SHIMA-R7/SHVC-SOUND-Player/SHVC-SOUND_python/spc_play.py

#!/usr/bin/env python3
"""
spc_play.py - .spcファイルをSHVC-SOUND(実チップ)で再生する

Arduino側は spc_uploader.ino (シリアルコマンド版) を書き込んでおくこと。

使い方:
    pip install pyserial
    python spc_play.py COM3 song.spc      (Windows)
    python spc_play.py /dev/ttyACM0 song.spc  (Linux)

.spcファイル形式(オフセットは既知の標準フォーマット):
    0x00-0x20 : ヘッダ("SNES-SPC700 Sound File Data v0.30" 等)
    0x25-0x26 : PC (リトルエンディアン)
    0x27      : A
    0x28      : X
    0x29      : Y
    0x2A      : PSW
    0x2B      : SP
    0x100-0x100FF : ARAM 64KB ダンプ
    0x10100-0x1017F : DSPレジスタ 128バイト
"""

import sys
import time
import serial

CMD_RESET = 0x01
CMD_SETADDR = 0x02
CMD_SENDBYTES = 0x03
CMD_READPORT = 0x04
CMD_SETVOLUME = 0x05
CMD_WRITEPORT = 0x0B

# 曲開始前の待ち合わせ(build_final_stub の port_handshake 参照)
STUB_MARK_STARTED = 0x99
STUB_MARK_WAITING = 0x98

ACK_RESET = 0x01
ACK_SETADDR = 0x02
ACK_CHUNK = 0x10
ACK_SENDBYTES = 0x03


class TransferCancelled(Exception):
    """転送がユーザー操作で中断されたことを示す。"""


def _decode_tag(raw: bytes) -> str:
    """ID666タグの文字列フィールドをデコードする。NUL以降は切り捨てる。"""
    raw = raw.split(b"\x00", 1)[0]
    for enc in ("cp932", "utf-8", "latin-1"):
        try:
            return raw.decode(enc).strip()
        except UnicodeDecodeError:
            continue
    return ""


class SpcFile:
    def __init__(self, path):
        with open(path, "rb") as f:
            data = f.read()
        if len(data) < 0x10180:
            raise ValueError(".spcファイルとして小さすぎます(壊れているかも)")

        # --- ID666タグ(あれば) ---
        # 0x23 が 26(0x1A) ならタグあり、27(0x1B) ならタグなし。
        # ここではテキスト形式のオフセットで読む(最も一般的な形式)。
        self.tags = {}
        if data[0x23] == 0x1A:
            self.tags = {
                "title": _decode_tag(data[0x2E:0x4E]),
                "game": _decode_tag(data[0x4E:0x6E]),
                "dumper": _decode_tag(data[0x6E:0x7E]),
                "comment": _decode_tag(data[0x7E:0x9E]),
                "date": _decode_tag(data[0x9E:0xA9]),
                "seconds": _decode_tag(data[0xA9:0xAC]),
                "artist": _decode_tag(data[0xB1:0xD1]),
            }

        self.pc = data[0x25] | (data[0x26] << 8)
        self.a = data[0x27]
        self.x = data[0x28]
        self.y = data[0x29]
        self.psw = data[0x2A]
        self.sp = data[0x2B]

        self.ram = data[0x100:0x100 + 0x10000]           # 64KB
        self.dsp = data[0x10100:0x10100 + 0x80]           # 128バイト


class SpcController:
    def __init__(self, port, baud=500000, log=None, progress=None):
        """
        log      : log(msg:str) 進行状況の文字列を受け取るコールバック
        progress : progress(done:int, total:int) 転送済み/全体バイト数
        いずれも省略時は標準出力へprint / 何もしない。
        """
        self.log = log if log is not None else print
        self.on_progress = progress if progress is not None else (lambda d, t: None)
        # 全体進捗の集計用。play()が転送開始前にtotal_bytesを設定する。
        self.total_bytes = 0
        self.done_bytes = 0

        self.ser = serial.Serial(port, baud, timeout=10)
        time.sleep(2)  # Arduinoのリセット待ち(DTRでリセットがかかる環境向け)
        self.ser.reset_input_buffer()

    def close(self):
        try:
            self.ser.close()
        except Exception:
            pass

    def _read_ack(self, expected):
        b = self.ser.read(1)
        if len(b) != 1 or b[0] != expected:
            raise RuntimeError(f"想定外の応答: {b!r} (期待値 0x{expected:02X})")

    def reset(self):
        self.log("SPC700をリセットしてready待ち...")
        self.ser.write(bytes([CMD_RESET]))
        self._read_ack(ACK_RESET)
        self.log("SPC700 ready.")

    def set_address(self, addr, continue_transfer):
        self.ser.write(bytes([CMD_SETADDR, addr & 0xFF, (addr >> 8) & 0xFF,
                               1 if continue_transfer else 0]))
        b = self.ser.read(1)
        if len(b) == 1 and b[0] == 0xEE:
            rest = self.ser.read(4)
            if len(rest) == 4 and rest[0] == 0xFF and rest[1] == 0xFF:
                raise RuntimeError(f"SETADDRがタイムアウト: addr=${addr:04X}")
            raise RuntimeError(f"SETADDR異常応答: {rest!r}")
        if len(b) != 1 or b[0] != ACK_SETADDR:
            raise RuntimeError(f"想定外の応答: {b!r} (期待値 0x{ACK_SETADDR:02X})")

    def send_bytes(self, data):
        length = len(data)
        self.ser.write(bytes([CMD_SENDBYTES, length & 0xFF, (length >> 8) & 0xFF]))

        diag = self.ser.read(3)
        if len(diag) != 3 or diag[0] != 0xAB:
            raise RuntimeError(f"len診断応答が異常: {diag!r} (送った長さ={length})")
        echoed_len = diag[1] | (diag[2] << 8)
        if echoed_len != length:
            raise RuntimeError(f"lenが化けた! 送った長さ={length}, Arduinoが受け取った長さ={echoed_len}")

        # Arduinoのシリアル受信バッファ(64バイト)を溢れさせないよう
        # PING_INTERVAL(Arduino側と一致させること)バイトずつ送って
        # 「まとめて1回だけ」確認応答を待つ。
        #
        # かつては1バイト送るごとに1往復のUSBシリアル通信が発生しており、
        # 実機計測で65216バイトの転送に約38秒かかっていた(バイト単位の
        # bit伝送時間ではなく、USB経由のシリアル往復レイテンシが支配的
        # だった)。往復回数を1/PING_INTERVALに減らすことで大幅に短縮する。
        PING_INTERVAL = 64
        pos = 0
        while pos < length:
            chunk_len = min(PING_INTERVAL, length - pos)
            self.ser.write(data[pos:pos + chunk_len])

            marker = self.ser.read(1)
            if len(marker) != 1:
                raise RuntimeError(f"応答なし(タイムアウト)。進捗={pos}/{length}")
            if marker[0] == 0xEE:
                rest = self.ser.read(4)
                idx = rest[0] | (rest[1] << 8)
                raise RuntimeError(
                    f"転送中にタイムアウト: バイト位置 {idx}/{length} で停止。"
                    f"送信した値=0x{rest[2]:02X}, 期待した応答=0x{idx & 0xFF:02X}, "
                    f"実際に読めた値=0x{rest[3]:02X}"
                )
            if marker[0] != 0xCD:
                raise RuntimeError(f"想定外の応答バイト: 0x{marker[0]:02X} (進捗={pos}/{length})")

            pos += chunk_len
            total = self.total_bytes or length
            self.on_progress(self.done_bytes + pos, total)
            if pos % (PING_INTERVAL * 5) == 0 or pos == length:
                self.log(f"    進捗: {pos}/{length} バイト転送済み")

        final = self.ser.read(1)
        if len(final) != 1 or final[0] != ACK_SENDBYTES:
            raise RuntimeError(f"最終応答が想定外: {final!r}")

    def write_block(self, addr, data):
        self.set_address(addr, True)
        self.send_bytes(data)

    def jump_to(self, addr):
        self.set_address(addr, False)

    def write_port(self, port, val):
        self.ser.write(bytes([CMD_WRITEPORT, port & 0x03, val & 0xFF]))
        b = self.ser.read(1)
        if len(b) != 1 or b[0] != CMD_WRITEPORT:
            raise RuntimeError(f"write_port応答が異常: {b!r} (spc_realtime.inoが古い可能性)")

    def wait_port(self, port, values, timeout=2.0):
        """ポートの値が values のどれかになるまで待ち、その値を返す。"""
        deadline = time.time() + timeout
        while True:
            v = self.read_port(port)
            if v in values or time.time() > deadline:
                return v

    def read_port(self, port):
        self.ser.write(bytes([CMD_READPORT, port]))
        resp = self.ser.read(2)
        if len(resp) != 2 or resp[0] != 0x04:
            raise RuntimeError(f"read_port応答が異常: {resp!r}")
        return resp[1]

    def set_volume(self, duty):
        """
        TDA7053AのVC1/VC2へつながるPWM(Arduino D10)のデューティ比を設定する。
        duty は 0(無音側)〜255(最大音量側)。R5/R6/C5の分圧値が未校正の場合、
        実際に0.4V以下/1.4V以上になる値は現物合わせで探る必要がある
        (PROJECT_BRIEF.md 3.4節・5節参照)。
        """
        duty = max(0, min(255, int(duty)))
        self.ser.write(bytes([CMD_SETVOLUME, duty]))
        resp = self.ser.read(2)
        if len(resp) != 2 or resp[0] != CMD_SETVOLUME:
            raise RuntimeError(f"set_volume応答が異常: {resp!r}")
        return resp[1]


def boost_master_volume(dsp: bytes, factor: float) -> bytes:
    """
    マスター音量(MVOLL/MVOLR)と各ボイスのVOLL/VOLRをまとめて底上げした
    DSPレジスタ配列を返す(元は変更しない)。

    S-DSPの音量レジスタは符号付き8bit(-128〜127)。正の値が大きいほど
    音量が大きい(負値は位相反転付きの音量で、曲データで意図的に使われる
    ことがあるため符号は保持する)。単純に factor 倍して、
    signed 8bit の範囲(-128〜127)でクランプする。

    マスター音量(MVOLL/MVOLR)は多くの曲で既に127(最大)近くまで
    使われているため、そこだけ底上げしても頭打ちで変化が出にくい。
    実際に鳴っている音量を支配しているのは各ボイスのVOLL/VOLR($x0/$x1,
    x=0-7のボイス番号)なので、そちらも同じ倍率で底上げする。
    """
    out = bytearray(dsp)
    regs = [0x0C, 0x1C]                              # MVOLL, MVOLR
    regs += [v * 0x10 + off for v in range(8) for off in (0x00, 0x01)]  # 各ボイスVOLL/VOLR
    for reg in regs:
        raw = dsp[reg]
        signed = raw - 256 if raw >= 128 else raw
        boosted = round(signed * factor)
        boosted = max(-128, min(127, boosted))
        out[reg] = boosted & 0xFF
    return bytes(out)


def handshake_values(spc: SpcFile):
    """
    曲開始前の待ち合わせに使う (開始合図, 最終的な$F4の値) を返す。
    開始合図は、曲が期待する$F4の値と必ず異なるものを選ぶ。
    """
    final_f4 = spc.ram[0xF4]
    signal = 0x5A if final_f4 != 0x5A else 0xA5
    return signal, final_f4


def build_final_stub(spc: SpcFile, force_test_tone: bool = False, volume_factor: float = 1.0,
                     port_handshake: bool = False) -> bytes:
    """
    DSPレジスタ128個・コントロール/タイマー・CPUレジスタをすべて復元して
    実行を開始する、SPC700側で実際に動くコード。

    メモリマップドI/O($F2/$F3等)への直接アドレス指定書き込みは信頼できない
    ことが実機で確認できたため、SPC700自身に「mov $F2,#idx / mov $F3,#val」を
    実行させる。このコードは高位アドレス($FFC0直下)に置く。

    ※既知の制限: スタブは約800バイトあり、$FFC0直下ということは
      $FC9x-$FFBF付近を占める。この領域はメインRAM転送($0100-$FFBF)の
      範囲内なので、曲データを800バイト分上書きしてしまう。
      この領域をサンプルデータやエコーバッファに使っている曲では
      ノイズや音の破綻が出る。要対策(スタブのループ化+テーブル参照で
      小型化する / エコーバッファ領域に置く 等)。

    最後に $00/$01 の実データを書き戻し、SP/PSW/A/X/Y を復元して
    本来のPCへジャンプする(Wikibooks "Loading SPC700 programs" の手法)。

    force_test_tone=True の場合、曲データ復元の直後に強制的にノイズテスト用の
    レジスタ上書きを追加する(診断用: 経路自体が生きているか確認するため)。
    """
    stub = bytearray()

    dsp = spc.dsp if volume_factor == 1.0 else boost_master_volume(spc.dsp, volume_factor)

    # 診断: スタブが実際に実行開始されたか確認するためのマーカー。
    # 実行されれば$F4(host側から見てport0)に0x99が現れるはず。
    stub += bytes([0x8F, 0x99, 0xF4])  # mov $F4,#0x99

    # DSPレジスタ128個を復元する。順序が重要:
    #  1. FLG($6C)にまず $20 を書く。soft reset(bit7)とmute(bit6)を解除しつつ、
    #     エコー書き込みは禁止(bit5=1)のままにする。ここで曲の保存値をそのまま
    #     書いてしまうと、ESA($6D)/EDL($7D)を設定する前にDSPがエコーデータを
    #     ARAMへ書き始め、転送済みの曲データを破壊する(特にEDL=0のときは
    #     エコーバッファ先頭4バイトを延々と上書きし続ける)。
    #  2. FLG/KON以外の126個を復元(この中でESA/EDLが正しい値になる)。
    #  3. KON($4C)を書いてキーオン。
    #  4. 最後にFLG($6C)へ保存値を書き、必要ならエコーを有効化する。
    stub += bytes([0x8F, 0x6C, 0xF2])
    stub += bytes([0x8F, 0x20, 0xF3])

    order = [i for i in range(0x80) if i not in (0x6C, 0x4C)] + [0x4C]
    for i in order:
        stub += bytes([0x8F, i, 0xF2])
        stub += bytes([0x8F, dsp[i], 0xF3])

    stub += bytes([0x8F, 0x6C, 0xF2])
    stub += bytes([0x8F, dsp[0x6C], 0xF3])

    # コントロールレジスタ・タイマー分周値を復元
    stub += bytes([0x8F, spc.ram[0xF1], 0xF1])
    stub += bytes([0x8F, spc.ram[0xFA], 0xFA])
    stub += bytes([0x8F, spc.ram[0xFB], 0xFB])
    stub += bytes([0x8F, spc.ram[0xFC], 0xFC])

    if force_test_tone:
        # 診断用: 以前成功したノイズテストと同じ強制上書き
        test_pokes = [
            (0x6C, 0x0A),  # FLG: mute=0,reset=0, ノイズクロック=0x0A
            (0x0C, 0x60),  # MVOLL
            (0x1C, 0x60),  # MVOLR
            (0x3D, 0x01),  # NON: ボイス0でノイズ有効
            (0x00, 0x7F),  # ボイス0 VOLL
            (0x01, 0x7F),  # ボイス0 VOLR
            (0x05, 0x00),  # ボイス0 ADSR1無効(GAIN直接モード)
            (0x07, 0x7F),  # ボイス0 GAIN最大
            (0x4C, 0x01),  # KON: ボイス0キーオン
        ]
        for idx, val in test_pokes:
            stub += bytes([0x8F, idx, 0xF2])
            stub += bytes([0x8F, val, 0xF3])
        # テストモードでは本来のCPUレジスタ復元・ジャンプはせず自己ループで停止
        stub += bytes([0x2F, 0xFE])  # BRA自己ループ
        return bytes(stub)

    if port_handshake:
        # 曲のプログラムは$F4-$F7を「ゲーム本体からの指示」として読む。
        # ジャンプ直後のポートにはIPL転送で使ったジャンプ先アドレス等が残っていて、
        # それを指示と解釈して壊れる曲がある(SimCity等。毎回同じ壊れ方をする)。
        # そこで曲へ飛ぶ前にホストを待ち、SPCファイルに記録された入力値を
        # 置いてもらってから開始する。
        #   1. $F4 に開始合図が来るまで待つ(ホストはその前に$F5-$F7を書く)
        #   2. $F4へ0x98を出して「待機中」を知らせる
        #   3. $F4 が曲の期待値になるまで待つ
        signal, final_f4 = handshake_values(spc)
        stub += bytes([0x78, signal, 0xF4, 0xD0, 0xFB])            # cmp $F4,#signal / bne 自分
        stub += bytes([0x8F, STUB_MARK_WAITING, 0xF4])             # mov $F4,#$98
        stub += bytes([0x78, final_f4, 0xF4, 0xD0, 0xFB])          # cmp $F4,#final / bne 自分

    # CPUレジスタ復元+ジャンプ
    # $00/$01 はメインRAM転送であえてスキップしている
    # (IPL ROMが転送中にこの2バイトを内部の転送先ポインタとして使うため)ので、
    # ここで実データを明示的に書き戻す。
    stub += bytes([0x8F, spc.ram[0x00], 0x00])   # mov $00,#byte0
    stub += bytes([0x8F, spc.ram[0x01], 0x01])   # mov $01,#byte1
    stub += bytes([0xCD, spc.sp])        # mov x,#sp
    stub += bytes([0xBD])                # mov sp,x
    stub += bytes([0xCD, spc.psw])       # mov x,#psw
    stub += bytes([0x4D])                # push x
    stub += bytes([0xE8, spc.a])         # mov a,#a
    stub += bytes([0xCD, spc.x])         # mov x,#x
    stub += bytes([0x8D, spc.y])         # mov y,#y
    stub += bytes([0x8E])                # pop psw
    stub += bytes([0x5F, spc.pc & 0xFF, (spc.pc >> 8) & 0xFF])  # jmp !abs pc

    return bytes(stub)


def play(port, spc_path, force_test_tone=False, skip_bulk=False, low_addr=False, only_stub=False,
         volume_factor=1.0, amp_volume=None, log=None, progress=None, cancelled=None):
    """
    log       : log(msg:str)                 進行状況の文字列
    progress  : progress(done:int, total:int) 転送済み/全体バイト数
    cancelled : cancelled() -> bool           Trueを返すと転送を中断する
    """
    log = log if log is not None else print
    spc = SpcFile(spc_path)
    ctl = SpcController(port, log=log, progress=progress)

    def check_cancel():
        if cancelled is not None and cancelled():
            raise TransferCancelled()

    try:
        ctl.reset()
        check_cancel()

        # 復元スタブを先に作っておく(全体バイト数を進捗表示に使うため)
        handshake = not force_test_tone
        stub = build_final_stub(spc, force_test_tone=force_test_tone,
                                volume_factor=volume_factor, port_handshake=handshake)

        head = spc.ram[0x0002:0x00F0]
        bulk = b"" if (skip_bulk or only_stub) else spc.ram[0x0100:0xFFC0]
        ctl.total_bytes = (0 if only_stub else len(head)) + len(bulk) + len(stub)

        if not only_stub:
            # 1. メインRAMダンプを転送 ($F0-$FFは飛ばす。I/Oレジスタ領域で単純書き込み不可)
            # 重要: $0000/$0001 はIPL ROMが転送中に内部の転送先ポインタとして使うため、
            # 通常のデータ転送で書き込んではいけない。ここは$0002からにする。
            log("RAM $0002-$00EF 転送中...")
            ctl.write_block(0x0002, head)
            ctl.done_bytes += len(head)
            check_cancel()

            if not skip_bulk:
                log("RAM $0100-$FFBF 転送中...")
                ctl.write_block(0x0100, bulk)
                ctl.done_bytes += len(bulk)
                check_cancel()
            else:
                log("(診断モード: RAM $0100-$FFBF 転送をスキップ)")
            # $FFC0-$FFFF (IPL ROMシャドウ領域) は転送不要
        else:
            log("(診断モード: スタブのみをリセット後最初の転送として送信)")

        # 2. DSPレジスタ・コントロール・タイマー・CPUレジスタをまとめて復元する
        #    実行コードを、曲データを壊さない高位アドレスに配置して実行する。
        log("復元スタブを構築・転送中...")
        if volume_factor != 1.0:
            log(f"マスター音量・各ボイス音量を{volume_factor:.2f}倍に変更(元の値からのブースト)")
        if low_addr:
            stub_addr = 0x0200
            log("  (診断モード: 低位アドレス$0200を使用)")
        else:
            stub_addr = 0xFFC0 - len(stub)
        log(f"  (スタブサイズ={len(stub)}バイト, 配置アドレス=${stub_addr:04X})")
        ctl.write_block(stub_addr, stub)
        ctl.done_bytes += len(stub)

        log("実行開始...")
        ctl.jump_to(stub_addr)

        if handshake:
            # スタブが動き出したのを確認してから、曲が期待する入力ポート値を置く
            signal, final_f4 = handshake_values(spc)
            p0 = ctl.wait_port(0, (STUB_MARK_STARTED, STUB_MARK_WAITING))
            if p0 not in (STUB_MARK_STARTED, STUB_MARK_WAITING):
                raise RuntimeError(f"復元スタブが動き出しません (port0=0x{p0:02X})")
            for p in (1, 2, 3):
                ctl.write_port(p, spc.ram[0xF4 + p])
            ctl.write_port(0, signal)
            p0 = ctl.wait_port(0, (STUB_MARK_WAITING,))
            if p0 != STUB_MARK_WAITING:
                raise RuntimeError(f"復元スタブが開始合図に応答しません (port0=0x{p0:02X})")
            ctl.write_port(0, final_f4)
            log("  入力ポートを曲の保存値 "
                + " ".join(f"{b:02X}" for b in spc.ram[0xF4:0xF8]) + " にして開始")
        else:
            time.sleep(0.1)
            p0 = ctl.read_port(0)
            log(f"  (診断: 実行開始マーカー確認 port0=0x{p0:02X}, 期待値=0x99)")

        if amp_volume is not None:
            actual = ctl.set_volume(amp_volume)
            log(f"アンプ音量(PWMデューティ比)を {actual}/255 に設定")

        log("再生開始しました。")
    finally:
        ctl.close()


def stop(port, log=None):
    """SHVC-SOUNDをリセットして再生を止める。"""
    log = log if log is not None else print
    ctl = SpcController(port, log=log)
    try:
        ctl.reset()
        log("再生を停止しました(SPC700をリセット)。")
    finally:
        ctl.close()


if __name__ == "__main__":
    if len(sys.argv) < 3:
        print(f"使い方: {sys.argv[0]} <シリアルポート> <spcファイル> "
              f"[--test] [--skip-bulk] [--low-addr] [--only-stub] [--volume N] [--amp-volume N]")
        print("  --volume N     : マスター/各ボイス音量(DSPレジスタ)をN倍にする。例: --volume 1.5")
        print("  --amp-volume N : TDA7053Aのアンプ段PWM音量を0-255で設定する(D10)。例: --amp-volume 180")
        sys.exit(1)
    flags = sys.argv[3:]
    test_mode = "--test" in flags
    skip_bulk_mode = "--skip-bulk" in flags
    low_addr_mode = "--low-addr" in flags
    only_stub_mode = "--only-stub" in flags
    volume_factor = 1.0
    if "--volume" in flags:
        volume_factor = float(flags[flags.index("--volume") + 1])
    amp_volume = None
    if "--amp-volume" in flags:
        amp_volume = int(flags[flags.index("--amp-volume") + 1])
    play(sys.argv[1], sys.argv[2], force_test_tone=test_mode, skip_bulk=skip_bulk_mode,
         low_addr=low_addr_mode, only_stub=only_stub_mode, volume_factor=volume_factor,
         amp_volume=amp_volume)
